jongarrison/NCV-ShakeIt/notes/shakeit_emptypcb.png

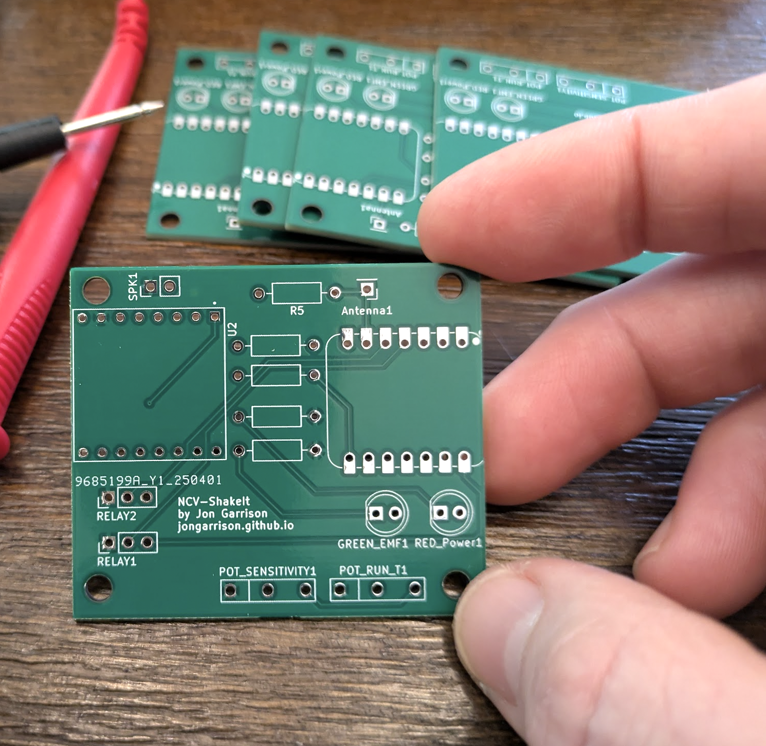
notes/shakeit_emptypcb.png
