jongarrison/NCV-ShakeIt/notes/shakeit_footprint.png

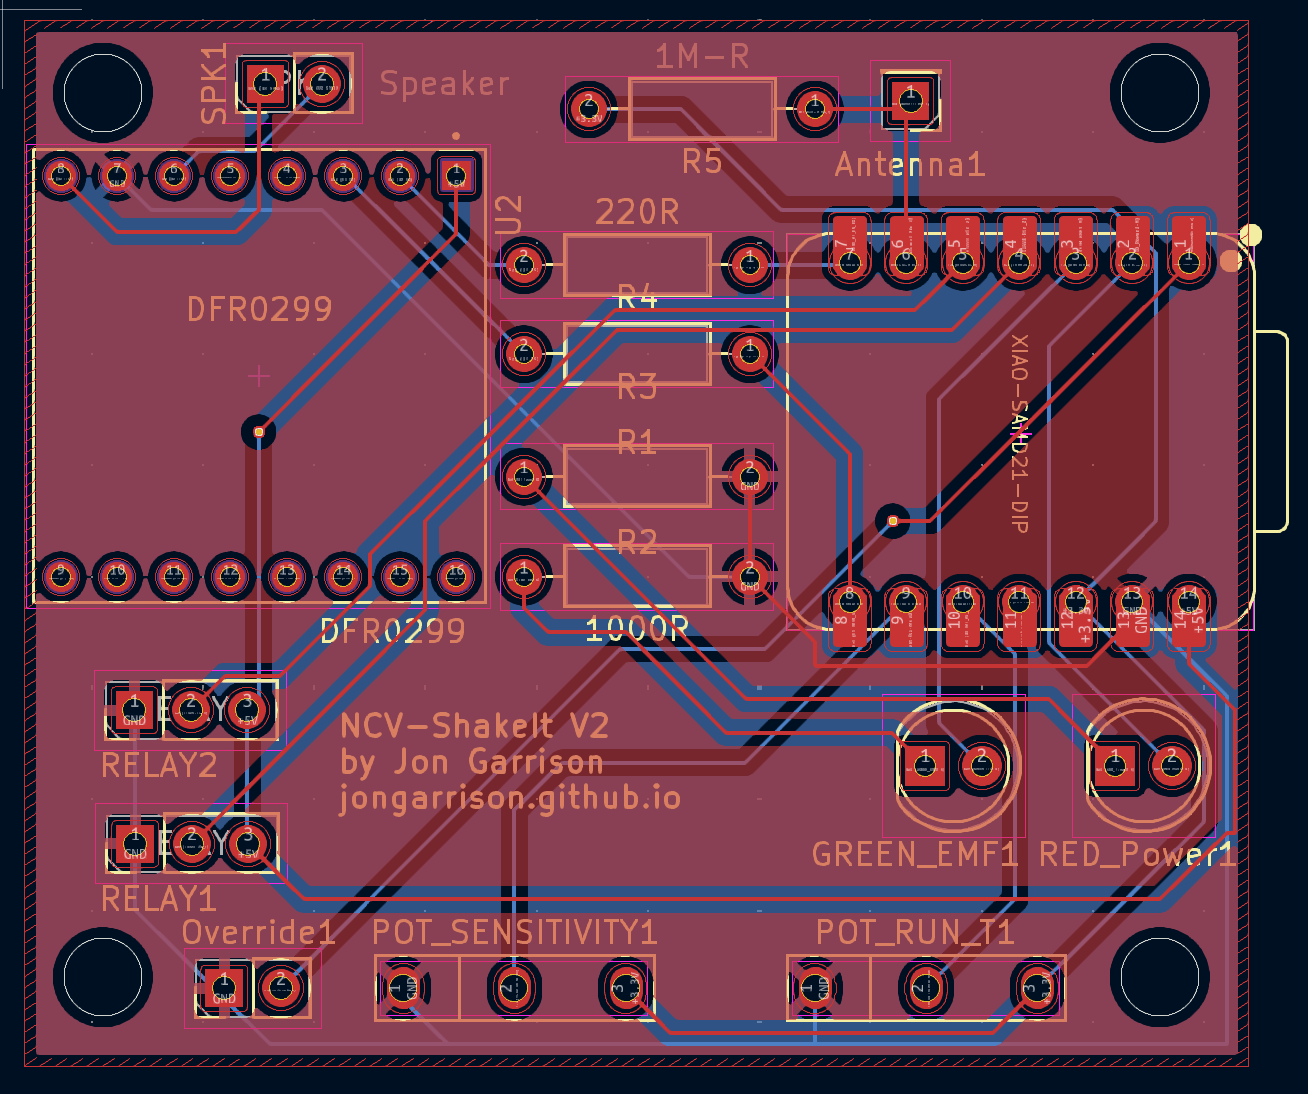
notes/shakeit_footprint.png
