jongarrison/NCV-ShakeIt/notes/shakeit_installed.jpg

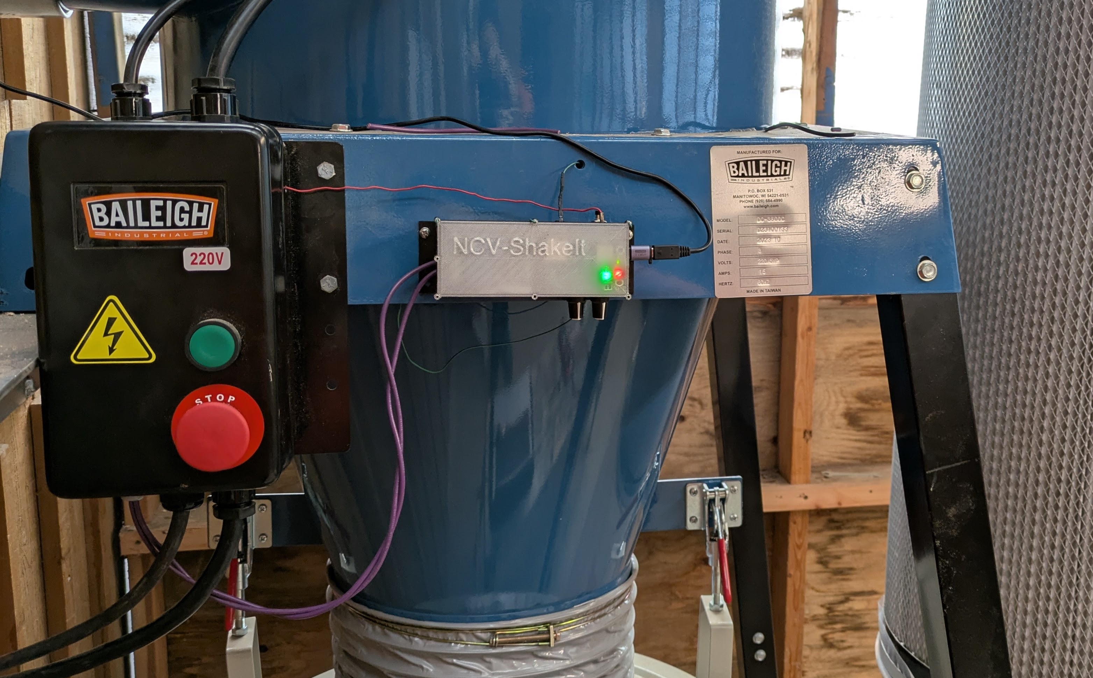
notes/shakeit_installed.jpg
