jongarrison/NCV-ShakeIt/notes/shakeit_installed_wide.jpg

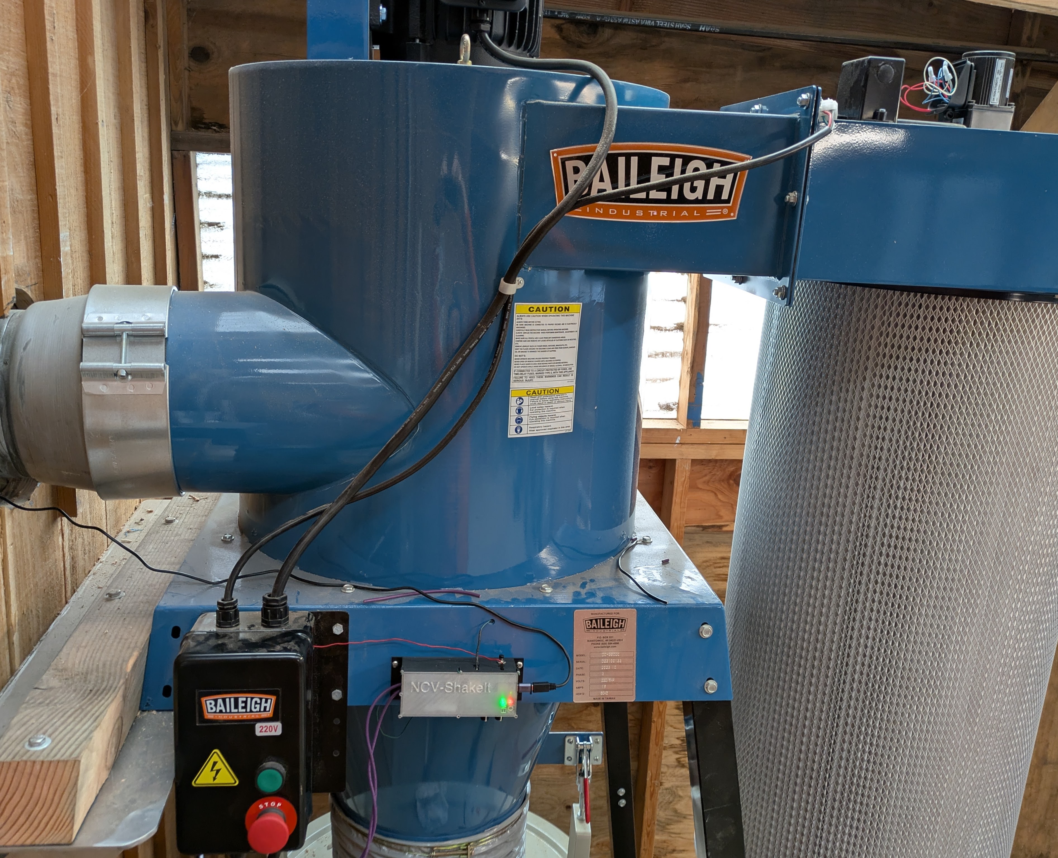
notes/shakeit_installed_wide.jpg
