jongarrison/NCV-ShakeIt/notes/shakeit_printing.jpg

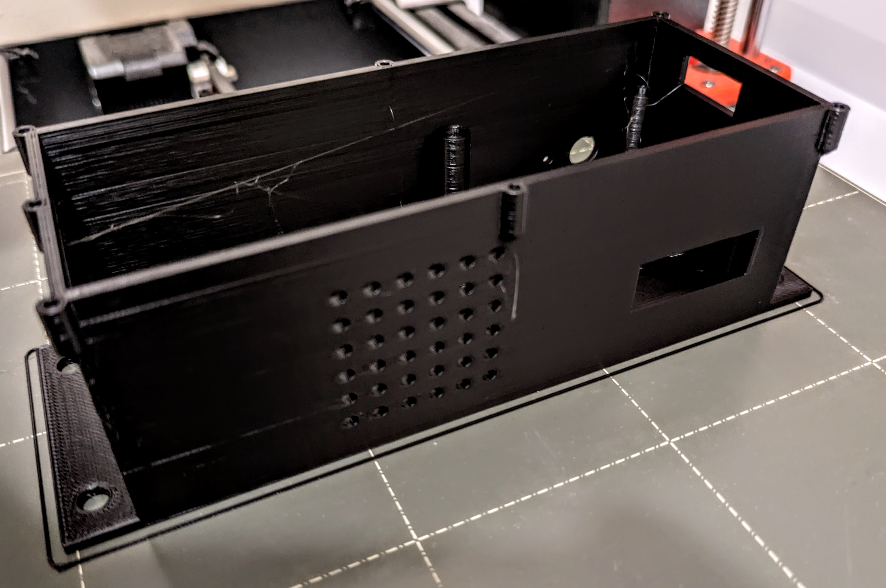
notes/shakeit_printing.jpg
