jongarrison/NCV-ShakeIt/notes/shakeit_soldered_board.jpg

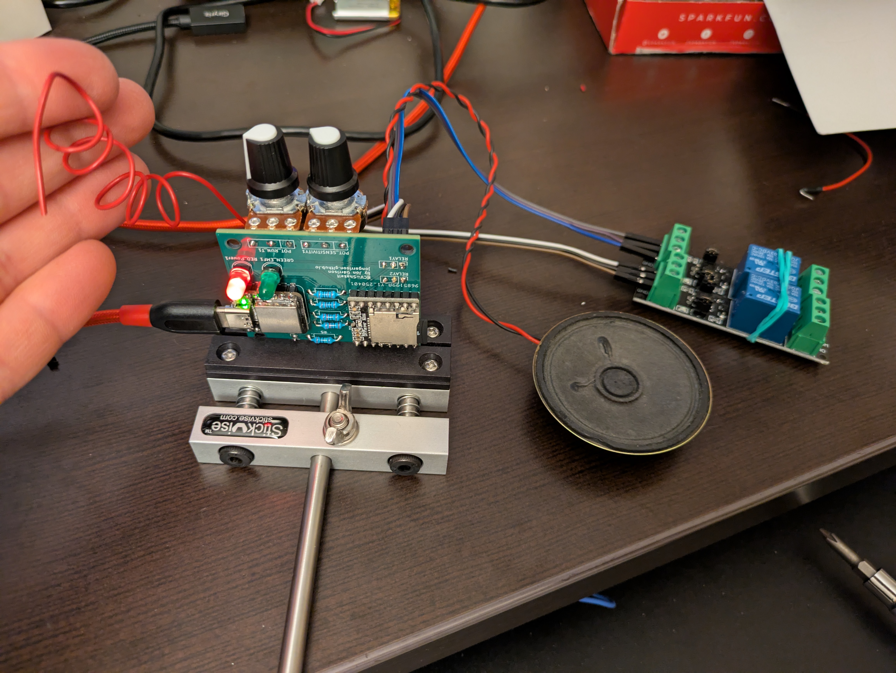
notes/shakeit_soldered_board.jpg
