jongarrison/NCV-ShakeIt/notes/shakeit_soldering.jpg

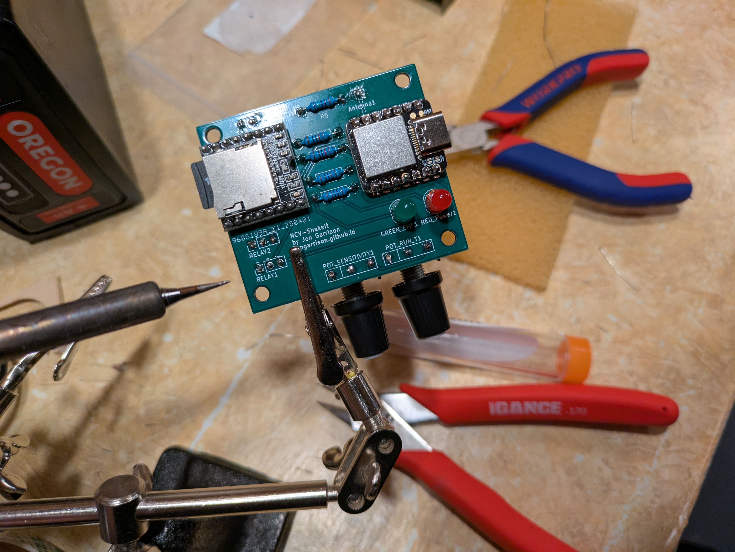
notes/shakeit_soldering.jpg
